rossumur/Arduinocade/music_tables.h

//
//  music_tables.h
//  CavernsSim
//
//  Created by Peter Barrett on 7/17/14.
//  Copyright (c) 2014 Peter Barrett. All rights reserved.
//

#ifndef CavernsSim_music_tables_h
#define CavernsSim_music_tables_h

/*
#include "math.h"
 static void dump(const char* s, int8_t* t)
 {
     printf("// %s\n",s);
     for (int i = 0; i < 256; i++) {
         printf("%4d,",*t++);
         if ((i & 0xF) == 0xF)
            printf("\n");
     }
 }

 static
 void make_audio_tables()
 {
    int8_t t[256];

    int i;
    for (i = 0; i < 256; i++)
        t[i] = sin(i*2*3.1415926535/256)*127;
    dump("Sine",t);

    for (i = 0; i < 256; i++)
        t[i] = i;
    dump("Sawtooth",t);

    for (i = 0; i < 256; i++)
    {
        t[i] = 127-(i << 1);
        if (i & 0x80)
            t[i] = -t[i];
    }
    dump("Triangle",t);

    for (i = 0; i < 256; i++)
        t[i] = i < 0x80 ? 127 : -127;
    dump("Square 50%",t);

     for (i = 0; i < 256; i++)
         t[i] = rand();
     dump("Random ",t);

    for (i = 0; i < 256; i++)
        t[i] = i < 0x40 ? 127 : -127;
    //dump("Square 25%",t);
 }
*/

PROGMEM
const int8_t _wave_tables[] = {
    //  Sine
    0,   3,   6,   9,  12,  15,  18,  21,  24,  27,  30,  33,  36,  39,  42,  45,
    48,  51,  54,  57,  59,  62,  65,  67,  70,  73,  75,  78,  80,  82,  85,  87,
    89,  91,  94,  96,  98, 100, 102, 103, 105, 107, 108, 110, 112, 113, 114, 116,
    117, 118, 119, 120, 121, 122, 123, 123, 124, 125, 125, 126, 126, 126, 126, 126,
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
    0x8837, // 120 8372.018555hz
    0x9051, // 121 8869.841797hz
    0x98E5, // 122 9397.274414hz
    0xA1FD, // 123 9956.063477hz
    0xAB9F, // 124 10548.079102hz
    0xB5D3, // 125 11175.305664hz
    0xC0A3, // 126 11839.821289hz
    0xCC18, // 127 12543.851562hz
};

#endif
