rossumur/Arduinocade/examples/pacman/pacman.h

// 64 tiles
PROGMEM
const uint8_t _tiles[] = {
    0x00,0x00,0x00,0x00,0xff,0xff,0x08,0x08,0x80,0x08,0x00,0x00,0x00,0x00,0x00,0x00,
    0x08,0x08,0x00,0x80,0x08,0x08,0x00,0x00,0x08,0x08,0x00,0x00,0x00,0x00,0x08,0x08,
    0x00,0x00,0x00,0x00,0x07,0x70,0x07,0x70,0x17,0x74,0x07,0x70,0x0b,0xb0,0x0b,0xb0,
    0x08,0x80,0x02,0x20,0x03,0x30,0x0d,0xd0,0x00,0x0a,0x00,0x00,0x00,0x00,0x00,0x00,
    0x08,0x08,0x08,0x08,0x00,0x00,0x00,0x08,0x00,0x00,0x00,0x00,0x00,0x00,0x08,0x00,
    0x00,0x08,0x00,0x00,0x00,0x00,0x00,0x00,0x00,0x00,0x00,0x00,0x00,0x00,0x00,0x00,
    0x0f,0x00,0x0f,0x00,0x0f,0x00,0x0f,0x00,0xf0,0xf0,0xff,0xf0,0x0f,0xf0,0xff,0xf0,
    0x0f,0x00,0x0f,0x00,0xff,0xc0,0xff,0xf0,0x3f,0xc0,0xff,0xc0,0xf0,0xf0,0xf0,0x00,
    0x00,0x00,0x00,0x00,0xff,0xff,0x88,0x08,0x00,0x08,0x02,0x88,0x88,0x80,0x88,0x88,
    0x08,0x08,0x08,0x08,0x08,0x08,0x88,0x88,0x88,0x08,0x88,0x00,0x00,0x28,0x08,0x00,
    0x00,0x00,0x00,0x00,0x77,0x77,0x77,0x77,0x77,0x77,0x77,0x00,0xbb,0xbb,0xbb,0xbb,
    0x88,0x88,0x22,0x22,0x33,0x33,0xdd,0xdd,0x00,0xa0,0x17,0xc0,0xff,0xff,0x00,0x00,
    0x08,0x08,0x88,0x08,0x00,0x28,0x00,0x08,0x8a,0x00,0x88,0x88,0x00,0x00,0x08,0x00,
    0x00,0x08,0x00,0x00,0x00,0x00,0x00,0x00,0x00,0x00,0x00,0x00,0x00,0x00,0x00,0x00,
    0xf0,0xf0,0xff,0x00,0xf0,0xf0,0xf0,0xf0,0xf0,0xf0,0xf0,0x00,0xf0,0x00,0x00,0xf0,
    0xf0,0xf0,0xf0,0xf0,0xf0,0xf0,0xf0,0x00,0xf0,0xf0,0xf0,0xf0,0xf0,0xf0,0xf0,0x00,
    0x00,0x00,0x00,0x00,0xff,0xff,0x00,0x00,0x00,0x08,0x08,0x00,0x00,0x08,0x00,0x00,
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
    (SPRITEPTR)ghost_write1,
    (SPRITEPTR)sprite_23,
    (SPRITEPTR)sprite_24,
    (SPRITEPTR)eye_ul,
    (SPRITEPTR)eye_ur,
    (SPRITEPTR)eye_dl,
    (SPRITEPTR)eye_dr,
    (SPRITEPTR)death_0,
    (SPRITEPTR)death_1,
    (SPRITEPTR)death_2,
    (SPRITEPTR)death_3,
};

enum {
    S_sprite_0, // 0
    S_sprite_1, // 1
    S_sprite_2, // 2
    S_sprite_3, // 3
    S_sprite_4, // 4
    S_sprite_5, // 5
    S_sprite_6, // 6
    S_sprite_7, // 7
    S_sprite_8, // 8
    S_sprite_9, // 9
    S_sprite_10, // 10
    S_sprite_11, // 11
    S_sprite_12, // 12
    S_sprite_13, // 13
    S_sprite_14, // 14
    S_sprite_15, // 15
    S_sprite_16, // 16
    S_sprite_17, // 17
    S_sprite_18, // 18
    S_sprite_19, // 19
    S_sprite_20, // 20
    S_ghost_blue0, // 21
    S_ghost_blue1, // 22
    S_ghost_white0, // 23
    S_ghost_write1, // 24
    S_sprite_23, // 25
    S_sprite_24, // 26
    S_eye_ul, // 27
    S_eye_ur, // 28
    S_eye_dl, // 29
    S_eye_dr, // 30
    S_death_0, // 31
    S_death_1, // 32
    S_death_2, // 33
    S_death_3, // 34
};
