rossumur/Arduinocade/examples/ballblaster/ballblaster_tiles.h

// 128 tiles
PROGMEM
const uint8_t _tiles[] = {
    0x00,0x00,0x00,0x00,0xff,0xff,0x00,0x00,0x00,0x00,0x00,0x00,0x00,0x00,0x00,0x00,
    0x00,0x00,0x00,0x00,0x00,0x00,0x00,0x00,0x00,0x00,0x00,0x00,0x00,0x00,0x00,0x00,
    0x00,0x00,0x00,0x00,0x00,0x00,0x50,0x00,0x00,0x50,0xdd,0xd8,0xdd,0xd0,0xdd,0xdf,
    0xdd,0xd0,0xbb,0xb1,0xbb,0xb0,0xbb,0xbf,0xbb,0xb0,0x00,0x00,0x00,0x00,0x00,0x00,
    0x00,0x00,0x00,0x00,0x00,0x00,0x00,0x00,0x00,0x00,0x00,0x00,0x00,0x00,0x05,0x05,
    0x00,0x00,0x00,0x00,0x00,0x00,0x00,0x00,0x00,0x00,0x00,0x00,0x00,0x00,0x00,0x00,
    0x05,0x00,0x05,0x00,0x00,0x05,0x00,0x00,0x05,0x05,0x05,0x00,0x05,0x05,0x00,0x00,
    0x00,0x05,0xdd,0x0d,0xd0,0xdd,0x0d,0xd0,0xdd,0x00,0x0d,0xd0,0xdd,0xdd,0xd0,0xd0,
    0x00,0x00,0x00,0x00,0x00,0x00,0x00,0x00,0x00,0x00,0x00,0x00,0x00,0x00,0x00,0x00,
    0x00,0x00,0x00,0x00,0x00,0x00,0x00,0x00,0x0d,0xd0,0x00,0x00,0x00,0x00,0x00,0x00,
    0x11,0x10,0x00,0x11,0x11,0x10,0x11,0x11,0x10,0x11,0x01,0x11,0x00,0x00,0x00,0xff,
    0xff,0x00,0xff,0xf0,0xff,0x0f,0xff,0xf0,0x00,0x00,0x00,0x00,0x00,0x00,0x00,0x00,
    0x00,0x00,0x00,0xff,0xff,0x00,0x00,0x0f,0xff,0xf0,0x00,0x00,0x00,0x00,0xf0,0x0f,
    0x00,0x00,0x00,0x00,0x00,0x00,0x00,0x00,0x00,0x00,0xff,0xff,0x00,0x00,0xff,0x00,
    0x00,0x0f,0xff,0x00,0xff,0x00,0xff,0xf0,0x00,0x00,0xff,0xff,0x00,0x00,0x0f,0xff,
    0xf0,0x0f,0xf0,0x0f,0xf0,0x0f,0xff,0x00,0x0f,0xff,0x00,0xff,0x00,0x00,0x0f,0xff,
    0x00,0x00,0x00,0x00,0xff,0xff,0x00,0x00,0x00,0x00,0x00,0x00,0x00,0x00,0x00,0x00,
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
    0x70,0x71,0x72,0x73,0x74,0x75,0x76,0x77,0x78,0x79,0x7a,0x7b,0x7c,0x7d,0x7e,0x7f,0x67,0x58,0x59,0x01,0x01,0x01,0x01,0x01,0x01,0x01,0x01,0x01,0x01,0x01,0x01,0x01,
};
