rossumur/Arduinocade/examples/jowst/jowst_tiles.h

// 72 tiles
PROGMEM
const uint8_t _tiles[] = {
0x00,0x00,0x00,0x00,0xff,0xff,0x33,0x33,0x33,0x33,0x33,0x33,0x00,0x00,0x33,0x33,
0x00,0x00,0x00,0x00,0x00,0x00,0x00,0x00,0x33,0x33,0x33,0x33,0x33,0x33,0x11,0x11,
0x33,0x33,0x33,0x33,0x33,0x33,0x33,0x33,0x11,0x13,0x11,0x33,0x00,0x00,0x33,0x33,
0x00,0x00,0x33,0x33,0x33,0x33,0x33,0x33,0x33,0x33,0x33,0x33,0x11,0x11,0x33,0x33,
0x33,0x33,0x33,0x35,0x31,0x11,0x22,0x22,0x33,0x22,0x22,0x33,0x07,0x60,0x00,0x00,
0x00,0x00,0x33,0x39,0x33,0x33,0x33,0x33,0x33,0x33,0x33,0x33,0x33,0x33,0x33,0x33,
0x3f,0xc0,0x1f,0x00,0x3f,0xc0,0x3f,0xc0,0xf0,0xf0,0xff,0xf0,0x1f,0x80,0xff,0xf0,
0x3f,0xc0,0x3f,0x80,0x15,0x55,0x55,0x55,0x55,0x55,0x55,0x51,0x00,0x00,0x00,0x00,
0x1f,0xff,0xff,0xff,0xff,0xff,0xff,0xf1,0x00,0x00,0x00,0x00,0x00,0x00,0x00,0x00,
0x00,0x00,0x00,0x00,0xff,0xff,0x33,0x33,0x33,0x33,0x33,0x33,0x00,0x00,0x33,0x33,
0x00,0x00,0x00,0x00,0x00,0x00,0x00,0x00,0x33,0x33,0x33,0x33,0x33,0x33,0x11,0x11,
0x33,0x33,0x33,0x33,0x11,0x11,0x11,0x31,0x13,0x33,0x01,0x13,0x00,0x00,0x13,0x33,
0x00,0x00,0x33,0x33,0x11,0x33,0x11,0x11,0x33,0x33,0x11,0x33,0x11,0x11,0x33,0x33,
0x03,0x33,0x33,0x33,0x33,0x11,0x2f,0x22,0x32,0x20,0x02,0x23,0x0f,0x70,0x00,0x00,
0x00,0x00,0x33,0x31,0x33,0x33,0x33,0x31,0x33,0x33,0x33,0x33,0x33,0x33,0x33,0x33,
0xf0,0xf0,0xff,0x00,0xf0,0xf0,0xf0,0xf0,0xf0,0xf0,0xf0,0x00,0xf0,0xf0,0x00,0xf0,
0xf0,0xf0,0xf0,0xf0,0x11,0xaa,0xaa,0xaa,0xaa,0xaa,0xaa,0x11,0x00,0x00,0x00,0x00,
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
const uint8_t leg0_right[] = {
0x07,0x02,0x00,0x00,
0x30,0x30,
0x30,0x30,
0x0f,0xfc,
0x00,0x33,
0x00,0x30,
0x00,0x30,
0x00,0x38,
};
PROGMEM
const uint8_t leg1_left[] = {
0x06,0x02,0x00,0x00,
0x03,0x30,
0x1c,0x30,
0x30,0x30,
0x30,0x30,
0x30,0x70,
0x01,0xc0,
};
PROGMEM
const uint8_t leg1_right[] = {
0x06,0x02,0x00,0x00,
0x03,0x30,
0x03,0x0e,
0x03,0x03,
0x03,0x03,
0x03,0x83,
0x00,0xe0,
};
PROGMEM
const uint8_t leg2_left[] = {
0x06,0x02,0x00,0x00,
0x03,0x1c,
0x03,0x0c,
0x07,0x03,
0x0e,0x03,
0x18,0x03,
0xf0,0x0f,
};
PROGMEM
const uint8_t leg2_right[] = {
0x06,0x04,0x00,0x00,
0x0e,0x30,0x00,0x00,
0x0c,0x30,0x00,0x00,
0x30,0x38,0x00,0x00,
0x30,0x1c,0x00,0x00,
0x30,0x06,0x00,0x00,
0x3c,0x03,0xc0,0x00,
};
PROGMEM
const uint8_t leg3_left[] = {
0x06,0x04,0x00,0x00,
0x03,0x0c,0x00,0x00,
0x03,0x06,0x00,0x00,
0x03,0x03,0x00,0x00,
0x03,0x03,0x00,0x00,
0x03,0x03,0x00,0x00,
0x0f,0x03,0xc0,0x00,
};
PROGMEM
const uint8_t leg3_right[] = {
0x06,0x04,0x00,0x00,
0x00,0xc3,0x00,0x00,
0x01,0x83,0x00,0x00,
0x03,0x03,0x00,0x00,
0x03,0x03,0x00,0x00,
0x03,0x03,0x00,0x00,
0x0f,0x03,0xc0,0x00,
};
PROGMEM
const uint8_t legskid_left[] = {
0x06,0x02,0x00,0x00,
0x03,0x06,
0x06,0x0c,
0x0c,0x18,
0x18,0x30,
0x30,0x60,
0xe1,0xc0,
};
PROGMEM
const uint8_t legskid_right[] = {
0x06,0x02,0x00,0x00,
0xc1,0x80,
0x60,0xc0,
0x30,0x60,
0x18,0x30,
0x0c,0x18,
0x07,0x0e,
};

SPRITEPTR _sprite_ptrs[] = {
(SPRITEPTR)bird0,
(SPRITEPTR)bird0_left,
(SPRITEPTR)bird0_flap,
(SPRITEPTR)bird0_flap_left,
(SPRITEPTR)bird1,
(SPRITEPTR)bird1_left,
(SPRITEPTR)bird1_flap,
(SPRITEPTR)bird1_flap_left,
(SPRITEPTR)bird2,
(SPRITEPTR)bird2_left,
(SPRITEPTR)bird2_flap,
(SPRITEPTR)bird2_flap_left,
(SPRITEPTR)bird2_white,
(SPRITEPTR)rider0,
(SPRITEPTR)rider0_left,
(SPRITEPTR)rider1,
(SPRITEPTR)rider1_left,
(SPRITEPTR)rider2,
(SPRITEPTR)rider2_left,
(SPRITEPTR)rider3,
(SPRITEPTR)rider3_left,
(SPRITEPTR)egg_0,
(SPRITEPTR)egg_1,
(SPRITEPTR)egg_2,
(SPRITEPTR)egg_crack,
(SPRITEPTR)explode0,
(SPRITEPTR)explode2,
(SPRITEPTR)explode1,
(SPRITEPTR)leg0_left,
(SPRITEPTR)leg0_right,
(SPRITEPTR)leg1_left,
(SPRITEPTR)leg1_right,
(SPRITEPTR)leg2_left,
(SPRITEPTR)leg2_right,
(SPRITEPTR)leg3_left,
(SPRITEPTR)leg3_right,
(SPRITEPTR)legskid_left,
(SPRITEPTR)legskid_right,
};

enum {
S_bird0, // 0
S_bird0_left, // 1
S_bird0_flap, // 2
S_bird0_flap_left, // 3
S_bird1, // 4
S_bird1_left, // 5
S_bird1_flap, // 6
S_bird1_flap_left, // 7
S_bird2, // 8
S_bird2_left, // 9
S_bird2_flap, // 10
S_bird2_flap_left, // 11
S_bird2_white, // 12
S_rider0, // 13
S_rider0_left, // 14
S_rider1, // 15
S_rider1_left, // 16
S_rider2, // 17
S_rider2_left, // 18
S_rider3, // 19
S_rider3_left, // 20
S_egg_0, // 21
S_egg_1, // 22
S_egg_2, // 23
S_egg_crack, // 24
S_explode0, // 25
S_explode2, // 26
S_explode1, // 27
S_leg0_left, // 28
S_leg0_right, // 29
S_leg1_left, // 30
S_leg1_right, // 31
S_leg2_left, // 32
S_leg2_right, // 33
S_leg3_left, // 34
S_leg3_right, // 35
S_legskid_left, // 36
S_legskid_right, // 37
};
