rossumur/Arduinocade/examples/titan/titan_tiles.h

// 162 tiles
PROGMEM
const uint8_t _tiles[] = {
    0x00,0x00,0x00,0x00,0x0f,0xc0,0x09,0xb9,0x01,0x00,0x00,0x01,0xbb,0x54,0x11,0x91,
    0x10,0x00,0x0f,0xf9,0x19,0x00,0x00,0x00,0x00,0x21,0x00,0x00,0x33,0x33,0x44,0x44,
    0x00,0x01,0x00,0x00,0x01,0x00,0x00,0x10,0x00,0x00,0x31,0x02,0x3f,0x33,0x33,0x32,
    0x44,0x44,0x44,0x44,0x44,0x44,0x55,0x55,0x33,0x33,0x33,0x33,0x22,0x22,0x44,0x44,
    0x00,0x3f,0xfc,0x00,0x04,0x44,0x44,0x44,0x44,0x40,0x7f,0xfe,0x00,0x28,0xa0,0x00,
    0x00,0x07,0x00,0x00,0x03,0x30,0x11,0x11,0x11,0x11,0x11,0x11,0x00,0xff,0xff,0x00,
    0xff,0xff,0xff,0xff,0x00,0x00,0x00,0x00,0x00,0x00,0x00,0x00,0x88,0x8f,0x88,0x88,
    0x1f,0x77,0x77,0x40,0x00,0x00,0xff,0x1f,0x1f,0x1f,0xf1,0xf1,0xff,0xf1,0xff,0xff,
    0x11,0x11,0x11,0x10,0x11,0x00,0x10,0x00,0x00,0x00,0x00,0x01,0x00,0x11,0x01,0x11,
    0x44,0x44,0x44,0x40,0x44,0x00,0x40,0x00,0x00,0x00,0x00,0x04,0x00,0x44,0x04,0x44,
    0x00,0x00,0x00,0x00,0x00,0x00,0x00,0x00,0x00,0x00,0x11,0x11,0x11,0x11,0x11,0x11,
    0xe0,0xe0,0x70,0x70,0x38,0x38,0x1c,0x1c,0x0e,0x0e,0x07,0x07,0x83,0x83,0xc1,0xc1,
    0x0f,0xc0,0x3f,0xf0,0xff,0xfc,0xfc,0xff,0xf0,0x3f,0xc0,0x0f,0x00,0x03,0x03,0x00,
    0x0f,0x60,0x0f,0x60,0x0f,0x60,0x0f,0x60,0x0f,0x60,0x0f,0x60,0x0f,0x60,0x0f,0x60,
    0x00,0x02,0x12,0x00,0x20,0x00,0x00,0x02,0x72,0x33,0x32,0x00,0x00,0x00,0x00,0x00,
    0x00,0x00,0x03,0x00,0x30,0x03,0x00,0x03,0x70,0x00,0x00,0x03,0x00,0x30,0x63,0x0c,
    0x37,0x7f,0xff,0xf7,0x37,0x73,0x7f,0xff,0x37,0x7f,0xff,0xf2,0x7f,0xff,0x37,0x7f,
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
    0x1c,0x00,
    0x06,0x10,
    0x15,0x00,
    0x47,0x00,
    0x03,0x40,
};
PROGMEM
const uint8_t spark_3[] = {
    0x04,0x02,0x00,0x00,
    0x00,0x00,
    0x07,0x00,
    0x07,0x00,
    0x01,0x00,
};
SPRITEPTR _sprite_ptrs[] = {
    (SPRITEPTR)ship,
    (SPRITEPTR)missile0,
    (SPRITEPTR)missile1,
    (SPRITEPTR)ship_explosion0,
    (SPRITEPTR)ship_explosion1,
    (SPRITEPTR)spark_0,
    (SPRITEPTR)spark_1,
    (SPRITEPTR)spark_2,
    (SPRITEPTR)spark_3,
};

enum {
    S_ship, // 0
    S_missile0, // 1
    S_missile1, // 2
    S_ship_explosion0, // 3
    S_ship_explosion1, // 4
    S_spark_0, // 5
    S_spark_1, // 6
    S_spark_2, // 7
    S_spark_3, // 8
};
