rossumur/Arduinocade/examples/pacman/pacman_music.h

//
//  pacman_music.h
//

//===============================================================
//===============================================================

const uint8_t _pacman_intro[] PROGMEM = {
    M_WAVE, (TRIANGLE << 4) | CH1 | CH2,
    M_ENVELOPE, (FADE2 << 4) | CH1 | CH2,
    M_NOTES_ON | 0x03,0x47,0x23,
    M_DELAY_4,
    M_NOTES_OFF | 0x01,
    M_DELAY_4,
    M_NOTES_OFF | 0x02,
    M_NOTES_ON | 0x01,0x53,
    M_DELAY_4,
    M_NOTES_OFF | 0x01,
    M_DELAY_5,
    M_NOTES_ON | 0x01,0x4e,
    M_DELAY_4,
    M_NOTES_OFF | 0x01,
    M_DELAY_4,
    M_NOTES_ON | 0x03,0x4b,0x2f,
    M_DELAY_4,
    M_NOTES_OFF | 0x01,
    M_DELAY_5,
    M_NOTES_OFF | 0x02,
    M_NOTES_ON | 0x03,0x53,0x23,
    M_DELAY_4,
    M_NOTES_ON | 0x01,0x4e,
    M_DELAY_4,
    M_NOTES_OFF | 0x03,
    M_DELAY_9,
    M_NOTES_ON | 0x01,0x4b,
    M_DELAY_9,
    M_NOTES_ON | 0x02,0x2f,
    M_DELAY_4,
    M_NOTES_OFF | 0x01,
    M_DELAY_4,
    M_NOTES_ON | 0x03,0x48,0x24,
    M_DELAY_4,
    M_NOTES_OFF | 0x01,
    M_DELAY_4,
    M_NOTES_OFF | 0x02,
    M_DELAY_1,
    M_NOTES_ON | 0x01,0x54,
    M_DELAY_4,
    M_NOTES_OFF | 0x01,
    M_DELAY_4,
    M_NOTES_ON | 0x01,0x4f,
    M_DELAY_4,
    M_NOTES_OFF | 0x01,
    M_DELAY_5,
    M_NOTES_ON | 0x03,0x4c,0x30,
    M_DELAY_4,
    M_NOTES_OFF | 0x01,
    M_DELAY_4,
    M_NOTES_ON | 0x03,0x54,0x24,
    M_DELAY_4,
    M_NOTES_OFF | 0x01,
    M_DELAY_1,
    M_NOTES_ON | 0x01,0x4f,
    M_DELAY_4,
    M_NOTES_OFF | 0x03,
    M_DELAY_9,
    M_NOTES_ON | 0x01,0x4c,
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

    M_SLIDE, CH3 | CH4, 256-1,256-1,
    M_DELAY_7,
    M_SLIDE, CH3 | CH4, 1,1,
    M_DELAY_5,

    M_SLIDE, CH3 | CH4, 256-1,256-1,
    M_DELAY_7,
    M_SLIDE, CH3 | CH4, 1,1,
    M_DELAY_5,

    M_SLIDE, CH3 | CH4, 256-1,256-1,
    M_DELAY_7,
    M_SLIDE, CH3 | CH4, 1,1,
    M_DELAY_5,

    // repeat for long death

    // Blerp Blerp at end
    M_NOTES_OFF | CH3,
    M_NOTES_ON | CH4, 58,
    M_SLIDE, CH3 | CH4, 4, 4,
    M_DELAY_10,
    M_NOTES_ON | CH4, 58,
    M_SLIDE, CH3 | CH4, 4, 4,
    M_DELAY_10,
    M_NOTES_OFF | CH3 | CH4,
    M_END
};

const uint8_t _extra_man[] PROGMEM = {
    M_WAVE, (SINE << 4) | CH3,
    M_WAVE, (TRIANGLE << 4) | CH4,
    M_ENVELOPE, (FADE3 << 4) | (CH3 | CH4),

    M_NOTES_ON | CH3, 66,
    M_NOTES_ON | CH4, 102,
    M_DELAY_12,

    M_NOTES_ON | CH3, 66,
    M_NOTES_ON | CH4, 102,
    M_DELAY_12,

    M_NOTES_ON | CH3, 66,
    M_NOTES_ON | CH4, 102,
    M_DELAY_12,

    M_NOTES_ON | CH3, 66,
    M_NOTES_ON | CH4, 102,
    M_DELAY_12,

    M_NOTES_ON | CH3, 66,
    M_NOTES_ON | CH4, 102,
    M_DELAY_12,

    M_NOTES_ON | CH3, 66,
    M_NOTES_ON | CH4, 102,
    M_DELAY_12,

    M_NOTES_ON | CH3, 66,
    M_NOTES_ON | CH4, 102,
    M_DELAY_12,
    M_NOTES_OFF | CH3 | CH4,
    M_END
};

                
