rossumur/Arduinocade/examples/jowst/jowst_music.h

    // Period is 18 frames
PROGMEM
const uint8_t _joust_start[] = {
    M_WAVE, (SQUARE << 4) | CH4,	// 16*7

    M_NOTES_ON | CH4, 84, // to 107
    M_SLIDE, CH4, 4,	// slide up
    M_DELAY_7,

    M_NOTES_ON | CH4, 84, // to 107
    M_VOLUME, CH4, 56,
    M_SLIDE, CH4, 4,	// slide up
    M_DELAY_7,

    M_NOTES_ON | CH4, 84, // to 107
    M_VOLUME, CH4, 48,
    M_SLIDE, CH4, 4,	// slide up
    M_DELAY_7,

    M_NOTES_ON | CH4, 84, // to 107
    M_VOLUME, CH4, 40,
    M_SLIDE, CH4, 4,	// slide up
    M_DELAY_7,

    M_NOTES_ON | CH4, 84, // to 107
    M_VOLUME, CH4, 32,
    M_SLIDE, CH4, 4,	// slide up
    M_DELAY_7,

    M_NOTES_ON | CH4, 84, // to 107
    M_VOLUME, CH4, 24,
    M_SLIDE, CH4, 4,	// slide up
    M_DELAY_7,

    M_NOTES_ON | CH4, 84, // to 107
    M_VOLUME, CH4, 16,
    M_SLIDE, CH4, 4,	// slide up
    M_DELAY_7,

    M_NOTES_ON | CH4, 84, // to 107
    M_VOLUME, CH4, 8,
    M_SLIDE, CH4, 4,	// slide up
    M_DELAY_7,

    M_NOTES_OFF | CH4,
    M_END
};

PROGMEM
const uint8_t _egg[] = {
    M_ENVELOPE, (FADE2 << 4) | CH4,
    M_WAVE, (SQUARE << 4) | CH4,
    M_NOTES_ON | CH4, 55,
    M_SLIDE, CH4, 1,
    M_DELAY_10,
    M_SLIDE, CH4, 3,
    M_DELAY_20,
    M_NOTES_OFF | CH4,
    M_END
};

PROGMEM
const uint8_t _thump[] = {
    M_WAVE, (SQUARE << 4) | CH4,
    M_NOTES_ON | CH4, 60, // ->44
    M_SLIDE, CH4, 256-6,
    M_DELAY_8,
    M_NOTES_OFF | CH4,
    M_END
};

PROGMEM
const uint8_t _buzzard[] = {
    M_WAVE, (RANDOM << 4) | CH4,
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
};


PROGMEM
const uint8_t _joustkill[] = {
    M_WAVE, (RANDOM << 4) | CH4,
    M_WAVE, (SQUARE << 4) | CH3,
    M_ENVELOPE, (FADE2 << 4) | CH3 | CH4,
    M_NOTES_ON | CH3 | CH4, 50, 128+32, //
    M_SLIDE, CH3 | CH4, 256-1,256-2,
    M_DELAY_20,
    M_NOTES_OFF | CH3 | CH4,
    M_END
};
